mark-v-d/motor_control/software/hal/etherdrive.cpp

#include "rtapi.h"
#ifdef RTAPI
#include "rtapi_app.h"
#endif
#include "hal.h"

static int comp_id;

#ifdef MODULE_INFO
MODULE_INFO(linuxcnc, const_cast<char*>("component:etherdrive:"));
//MODULE_INFO(linuxcnc, const_cast<char*>("pin:out:float:0:out::None:None"));
MODULE_INFO(linuxcnc, const_cast<char*>("param:value:float:0:r::1.0:None"));
MODULE_INFO(linuxcnc, const_cast<char*>("funct:sync:1:"));
MODULE_INFO(linuxcnc, const_cast<char*>("license:GPL"));
MODULE_LICENSE("GPL");
#endif // MODULE_INFO


#include <sys/io.h>

#include "raw_socket.h"
#include "drive_io.h"
#include <vector>

constexpr std::array<uint8_t,6> bcast_mac{255,255,255,255,255,255};
constexpr std::array<uint8_t,4> bcast_ip{255,255,255,255};

std::array<std::array<uint8_t,6>,16> mac;

raw_socket skt;
constexpr uint16_t base=0xec00;

/******************************************************************************/
struct comp_state {
    // input pins
    hal_float_t *Iset[2];
    hal_bit_t *enable;
    hal_bit_t *digout[2];
    hal_u32_t *encoder;
    hal_u32_t *poles;
    hal_float_t *angle_offset;
    hal_float_t *limit[2];
    hal_float_t *P;
    hal_float_t *I;
    hal_float_t *L;
    hal_float_t *overvoltage;
    hal_float_t *overcurrent;

    // output pins
    hal_s32_t *position;
    hal_s32_t *position2;
    hal_s32_t *index;
    hal_s32_t *index2;
    hal_float_t *Irotor[2];
    hal_float_t *Vrotor[2];
    hal_float_t *angle;
    hal_float_t *Vservo;
    hal_u32_t *encoder_invalid;
    hal_u32_t *encoder_missing;
    hal_u32_t *pending;
    hal_u32_t *drive_rx;
    hal_s32_t *timer_delta;
    hal_s32_t *dt;
    hal_bit_t *digin[2];
    hal_u32_t *digin_all;
    hal_bit_t *unconfigured;
    hal_float_t *vthermistor;

    bool valid;
    double thermistor=0;
    static constexpr double thermistor_gain=1e-3;

    void init(int i) {
	std::string prefix="etherdrive."+std::to_string(i)+".";
	auto pin=[&](hal_pin_dir_t dir,std::string name, auto p) {
	    *p=nullptr;
	    using T=decltype(p);
	    if constexpr(std::is_same_v<T,hal_float_t**>)
		return hal_pin_float_new((prefix+name).c_str(),dir,p,comp_id);
	    else if constexpr(std::is_same_v<T,hal_s32_t**>)
		return hal_pin_s32_new((prefix+name).c_str(),dir,p,comp_id);
	    else if constexpr(std::is_same_v<T,hal_u32_t**>)
		return hal_pin_u32_new((prefix+name).c_str(),dir,p,comp_id);
	    else if constexpr(std::is_same_v<T,hal_bit_t**>)
		return hal_pin_bit_new((prefix+name).c_str(),dir,p,comp_id);
	    else
		return 1;
	};
	int ok=
	    !pin(HAL_IN, "Iset-0", &Iset[0]) &&
	    !pin(HAL_IN, "Iset-1", &Iset[1]) &&
	    !pin(HAL_IN, "enable", &enable) &&
	    !pin(HAL_OUT,"position", &position) &&
	    !pin(HAL_OUT,"position2", &position2) &&
	    !pin(HAL_OUT,"index", &index) &&
	    !pin(HAL_OUT,"index2", &index2) &&
	    !pin(HAL_OUT,"Irotor-0", &Irotor[0]) &&
	    !pin(HAL_OUT,"Irotor-1", &Irotor[1]) &&
	    !pin(HAL_OUT,"Vrotor-0", &Vrotor[0]) &&
	    !pin(HAL_OUT,"Vrotor-1", &Vrotor[1]) &&
	    !pin(HAL_OUT,"angle", &angle) &&
	    !pin(HAL_OUT,"Vservo", &Vservo) &&
	    !pin(HAL_OUT,"encoder_invalid", &encoder_invalid) &&
	    !pin(HAL_OUT,"encoder_missing", &encoder_missing) &&
	    !pin(HAL_OUT,"pending", &pending) &&
	    !pin(HAL_OUT,"drive_rx", &drive_rx) &&
	    !pin(HAL_OUT,"timer_delta", &timer_delta) &&
	    !pin(HAL_IN,"digout-0", &digout[0]) &&
	    !pin(HAL_IN,"digout-1", &digout[1]) &&
	    !pin(HAL_OUT,"digin-0", &digin[0]) &&
	    !pin(HAL_OUT,"digin-1", &digin[1]) &&
	    !pin(HAL_OUT,"digin-all", &digin_all) &&
	    !pin(HAL_OUT,"unconfigured", &unconfigured) &&
	    !pin(HAL_OUT,"vthermistor", &vthermistor) &&
	    !pin(HAL_OUT,"timer_error", &dt) &&
	    !pin(HAL_IN,"encoder", &encoder) &&
	    !pin(HAL_IN,"poles", &poles) &&
	    !pin(HAL_IN,"angle_offset", &angle_offset) &&
	    !pin(HAL_IN,"limit-0", &limit[0]) &&
	    !pin(HAL_IN,"limit-1", &limit[1]) &&
	    !pin(HAL_IN,"P", &P) &&
	    !pin(HAL_IN,"I", &I) &&
	    !pin(HAL_IN,"L", &L) &&
	    !pin(HAL_IN,"overvoltage", &overvoltage) &&
	    !pin(HAL_IN,"overcurrent", &overcurrent)
	    ;
	if(ok)
	    *unconfigured=1;
    }

    void update(motion_ns::to_host &buffer){
	*position=buffer.position;
	*index=buffer.index;
	*position2=buffer.position2;
	*index2=buffer.index2;
	*Irotor[0]=buffer.Irotor[0];
	*Irotor[1]=buffer.Irotor[1];
	*Vrotor[0]=buffer.Vrotor[0];
	*Vrotor[1]=buffer.Vrotor[1];
	*angle=buffer.angle;
	*Vservo=buffer.Vservo;
	*encoder_invalid=buffer.encoder_invalid;
	*encoder_missing=buffer.encoder_missing;
	*timer_delta=buffer.timer_delta;
	*digin[0]=!(buffer.digin&1);
	*digin[1]=!((buffer.digin>>1)&1);
	*digin_all=buffer.digin;
	*dt=buffer.timer_error;
	*drive_rx=buffer.counter;
	thermistor+=thermistor_gain*((4095-buffer.tpower)*3.3/4095-thermistor);
	*vthermistor=thermistor;
	(*pending)=0;
    }

    void config_complete() {
	*unconfigured=0;
    }
};

std::vector<comp_state*> state;

static void send(void *p, long period)
{
    for(int i=0; i<state.size(); i++) {
	std::array<uint8_t,4> ip{192,168,0,uint8_t(i+1)};
	auto s=*state[i];
	if((*state[i]->unconfigured)) {
	    config_ns::to_drive d{
		.led=0,
		.encoder=int(*state[i]->encoder),
		.poles=int(*state[i]->poles),
		.angle_offset=float(*state[i]->angle_offset),
		.current_P=float(*state[i]->P),
		.current_I=float(*state[i]->I),
		.current_L=float(*state[i]->L),
		.overvoltage=float(*state[i]->overvoltage),
		.overcurrent=float(*state[i]->overcurrent)
	    };
	    skt.send(config_ns::send_t(skt, mac[i], ip, d));
	    continue;
	}
	std::complex<float> I{
	    float(*state[i]->Iset[0]),
	    float(*state[i]->Iset[1])
	};
	std::complex<float> limit{
	    float(*state[i]->limit[0]),
	    float(*state[i]->limit[1])
	};
	uint32_t dout=*state[i]->digout[0] | (*state[i]->digout[1]<<1);
	if(*state[i]->enable)
	    dout|=motion_ns::to_drive::DRIVE_ENABLE;
	skt.send(motion_ns::send_t(skt, mac[i], ip, I, limit, dout));
	if((*state[i]->pending)>10) {
	    (*state[i]->unconfigured)=1;
	    (*state[i]->pending)=10;
	}
	(*state[i]->pending)++;
    }
}

static void sync(void *p, long period)
{
    static struct timespec timestamp{0,0};
    if(!timestamp.tv_sec) {
	if(clock_gettime(CLOCK_MONOTONIC, &timestamp)) {
	    perror("clock_gettime");
	}
    } else {
	timestamp.tv_nsec+=period;
	while(timestamp.tv_nsec>=1'000'000'000) {
	    timestamp.tv_sec++;
	    timestamp.tv_nsec-=1'000'000'000;
	}
    }

    auto ts=timestamp;
    ts.tv_nsec+=period;
    while(ts.tv_nsec>=1'000'000'000) {
	ts.tv_sec++;
	ts.tv_nsec-=1'000'000'000;
    }

    outb(0,base);
    skt.send(sync_ns::send_t(skt,bcast_mac,bcast_ip,timestamp,ts));
    outb(1,base);

    ssize_t rx_size;
    do {
	union rx_types {
	    udp_t udp;
	    sync_ns::recv_t sync;
	    motion_ns::recv_t motion;
	    char txt[1024];
	} buffer;
	rx_size=recv(skt.socket(), &buffer, sizeof(buffer), MSG_DONTWAIT);
	unsigned index=buffer.udp.src_ip[3]-1;
	if(index>=state.size())
	    continue;
	if(buffer.udp.src_port==htons(motion_ns::port)
	    && rx_size==sizeof(buffer.motion) && index<state.size()
	) {
	    state[index]->update(buffer.motion);
	} else if(buffer.udp.src_port==htons(config_ns::port)) {
	    state[index]->config_complete();
	}
    } while(rx_size>0);
    outb(255,base);
}


////////////////////////////////////////////////////////////////////////////////
static char *names[16] = {0,};
static char const *device="eth1";

RTAPI_MP_STRING(device, "ethernet device");
RTAPI_MP_ARRAY_STRING(names, 16, "mac addresses of etherdrives");

extern "C" int rtapi_app_main(void)
{
    int r = 0;
    int i;
    comp_id = hal_init("etherdrive");
    if(comp_id < 0)
	return comp_id;
    if(ioperm(base, 8, 1)) {
	perror("request_region failed\n");
	return -1;
    }


    for(int i=0; names[i] && i<16; i++) {
	std::array<unsigned,6> d;
	char na[100];
	strcpy(na,names[i]);
	if(sscanf(na,"%x:%x:%x:%x:%x:%x:%x",
	    &d[0],&d[1],&d[2],&d[3],&d[4],&d[5])!=6
	) {
	    rtapi_print_msg(RTAPI_MSG_ERR, "invalid mac address: %s",names[i]);
	    return -EINVAL;
	};
	for(int j=0; j<d.size(); j++) {
	    if(d[j]>255) {
		rtapi_print_msg(RTAPI_MSG_ERR, "invalid mac address: %s",
		    names[i]);
		return -EINVAL;
	    }
	    mac[i][j]=d[j];
	}
        auto p=reinterpret_cast<comp_state*>(hal_malloc(sizeof(comp_state)));
        p->init(i);
	state.push_back(p);
    }

    try {
	skt.init(device);
    } catch (std::string const &s) {
        rtapi_print_msg(RTAPI_MSG_ERR, "Cannot open device");
        return -EINVAL;
    }

    // Export the send-sync function
    if(!r)
	r = hal_export_funct("etherdrive.sync", sync, NULL, 1, 0, comp_id);
    if(!r)
	r = hal_export_funct("etherdrive.send", send, NULL, 1, 0, comp_id);
    if(r) {
        hal_exit(comp_id);
    } else {
        hal_ready(comp_id);
    }
    return r;
}

extern "C" void rtapi_app_exit(void)
{
    hal_exit(comp_id);
}
