mark-v-d/motor_control/software/xmc4400/lathe/lathe_cmds.hal

# Mon Jan 23 14:18:18 CET 2017
#
# This file:    ./lathe_cmds.hal
# Created by:   /usr/src/linuxcnc/lib/hallib/basic_sim.tcl
# With options: 
# From inifile: /home/mark/.emc/lathe.ini
#
# This file contains the hal commands produced by basic_sim.tcl
# (and any hal commands executed prior to its execution).
#
# To use ./lathe_cmds.hal in the original inifile (or a copy of it),
# edit to change:
#     [HAL]
#     HALFILE = LIB:basic_sim.tcl parameters
# to:
#     [HAL]
#     HALFILE = ./lathe_cmds.hal
#
# Note: Inifile Variables substitutions specified in the inifile
#       and interpreted by halcmd are automatically substituted
#       in the created halfile (./lathe_cmds.hal).
#

# user space components
loadusr -W hal_manualtoolchange

# components
loadrt trivkins coordinates=xz 
loadrt motmod base_period_nsec=222222 servo_period_nsec=222222 num_joints=2 
#loadrt __base-thread  (not loaded by loadrt, no args saved)
#loadrt __servo-thread  (not loaded by loadrt, no args saved)
loadrt pid names=J0_pid,J1_pid 
loadrt mux2 names=J0_mux,J1_mux 
loadrt ddt names=J0_vel,J0_accel,J1_vel,J1_accel 
loadrt sim_home_switch names=J0_switch,J1_switch 
loadrt sim_spindle names=sim_spindle 
loadrt limit2 names=limit_speed 
loadrt lowpass names=spindle_mass 
loadrt near names=near_speed 
loadrt etherdrive names=J0_drive,J1_drive ipaddr="192.168.0.5","192.168.0.4"

# pin aliases
# param aliases
# signals
newsig tool:change-loop bit  
# nets
net J0:acc J0_accel.out
net J0:enable joint.0.amp-enable-out => J0_pid.enable
net J0:homesw J0_switch.home-sw => joint.0.home-sw-in
net J0:on-pos J0_pid.output => J0_mux.in1
#net J0:pos-cmd joint.0.motor-pos-cmd => J0_pid.command
net J0:vel J0_vel.out => J0_accel.in

net J1:acc J1_accel.out
net J1:enable joint.1.amp-enable-out => J1_pid.enable
net J1:homesw J1_switch.home-sw => joint.1.home-sw-in
net J1:on-pos J1_pid.output => J1_mux.in1
net J1:pos-cmd joint.1.motor-pos-cmd => J1_pid.command
net J1:pos-fb J1_mux.out => J1_mux.in0 J1_switch.cur-pos J1_vel.in joint.1.motor-pos-fb
net J1:vel J1_vel.out => J1_accel.in

net estop:loop iocontrol.0.user-enable-out => iocontrol.0.emc-enable-in
net sample:enable J0_mux.sel J1_mux.sel motion.motion-enabled
net spindle-at-speed near_speed.out => motion.spindle-at-speed
net spindle-index-enable motion.spindle-index-enable <=> sim_spindle.index-enable
net spindle-pos sim_spindle.position-fb => motion.spindle-revs
net spindle-rpm-filtered spindle_mass.out => motion.spindle-speed-in near_speed.in2
net spindle-speed-cmd motion.spindle-speed-out => limit_speed.in near_speed.in1
net spindle-speed-limited limit_speed.out => sim_spindle.velocity-cmd spindle_mass.in

net tool:change iocontrol.0.tool-change => hal_manualtoolchange.change
net tool:changed hal_manualtoolchange.changed => iocontrol.0.tool-changed
net tool:prep-loop iocontrol.0.tool-prepare => iocontrol.0.tool-prepared
net tool:prep-number iocontrol.0.tool-prep-number => hal_manualtoolchange.number
# parameter values
setp J0_accel.tmax            0
setp J0_mux.tmax            0
setp J0_pid.do-pid-calcs.tmax            0
setp J0_switch.tmax            0
setp J0_vel.tmax            0
setp J1_accel.tmax            0
setp J1_mux.tmax            0
setp J1_pid.do-pid-calcs.tmax            0
setp J1_switch.tmax            0
setp J1_vel.tmax            0
#setp base-thread.tmax            0
setp limit_speed.tmax            0
setp motion-command-handler.tmax            0
setp motion-controller.tmax            0
setp near_speed.difference           10
setp near_speed.scale          1.1
setp near_speed.tmax            0
setp servo-thread.tmax            0
setp sim_spindle.scale   0.01666667
setp sim_spindle.tmax            0
setp spindle_mass.gain         0.07
setp spindle_mass.tmax            0

# realtime thread/function links
addf etherdrive.sync servo-thread
addf motion-command-handler servo-thread
addf motion-controller servo-thread
addf J0_pid.do-pid-calcs servo-thread
addf J1_pid.do-pid-calcs servo-thread
addf J0_mux servo-thread
addf J1_mux servo-thread
addf J0_vel servo-thread
addf J0_accel servo-thread
addf J1_vel servo-thread
addf J1_accel servo-thread
addf J0_switch servo-thread
addf J1_switch servo-thread
addf limit_speed servo-thread
addf spindle_mass servo-thread
addf near_speed servo-thread
addf sim_spindle servo-thread
addf etherdrive.control servo-thread

# setp commands for unconnected input pins
setp J0_pid.FF0 1.0
setp J0_pid.Pgain 0
setp J0_pid.Dgain 0
setp J0_pid.Igain 0
setp J0_pid.FF1 0
setp J0_pid.FF2 0

setp J0_drive.kP-0 0.1
setp J0_drive.kP-1 0.1
setp J0_drive.kI-0 0.1
setp J0_drive.kI-1 0.1

setp J1_pid.FF0 1.0
setp J1_pid.Pgain 0
setp J1_pid.Dgain 0
setp J1_pid.Igain 0
setp J1_pid.FF1 0
setp J1_pid.FF2 0

setp J0_switch.hysteresis 0.05
setp J0_switch.home-pos 0.10
setp J1_switch.hysteresis 0.05
setp J1_switch.home-pos 0.10
setp sim_spindle.scale 0.01666667
setp limit_speed.maxv 5000.0
setp spindle_mass.gain .07
setp near_speed.scale 1.1
setp near_speed.difference 10

setp J1_drive.kP-0 0.1
setp J1_drive.kP-1 0.1
setp J1_drive.kI-0 0.1
setp J1_drive.kI-1 0.1
