mark-v-d/motor_control/software/rt/motion_setpoints.cpp

/*
 *  This program is free software: you can redistribute it and/or modify
 *  it under the terms of the GNU General Public License as published by
 *  the Free Software Foundation, either version 3 of the License, or
 *  (at your option) any later version.
 */

#include <chrono>
#include <complex>
#include <fstream>
#include <iostream>
#include <limits.h>
#include <pthread.h>
#include <sched.h>
#include <sys/io.h>
#include <sys/mman.h>

#include "drive_io.h"
#include "ss.h"

using namespace std::complex_literals;
using namespace std::chrono_literals;

std::array<uint8_t,6> mac{0xc2, 0x00, 0x85, 0x0c, 0x10, 0xc0}; // X
//constexpr std::array<uint8_t,6> mac{0xc2, 0x00, 0x8d, 0x11, 0x11, 0xc0}; // Z
//constexpr std::array<uint8_t,6> mac{0xc2, 0x00, 0x86, 0x05, 0x10, 0xc0}; // T
constexpr std::array<uint8_t,4> ip{192,168,0,6};

constexpr std::complex<float> limit{0.44,0.75};

using timebase_t=std::chrono::duration<int,std::ratio<1,4500>>;

constexpr int order=3;
constexpr int inputs=2;
constexpr int outputs=1;

ss_t<order,inputs,outputs> controller;

std::array<double,2> scale{1,1};

struct sync_I_t:public sync_t {
    std::complex<float> I;
    decltype(controller)::input_t setpoint;
    decltype(controller)::input_t error;
};
std::vector<sync_I_t> table;

std::ostream &operator<<(std::ostream &s, sync_I_t const &d) {
    s	<< sync_t(d)
	<< " " << real(d.I) << " " << imag(d.I)			// 34,35
	<< " " << d.setpoint(0,0) << " " << d.setpoint(1,0)	// 36,37
	<< " " << d.error(0,0) << " " << d.error(1,0)		// 38,39
	<< " " << d.timer_error					// 40
	<< " " << d.counter					// 41
	<< " " << d.timer_delta					// 42
	;
    return s;
}

raw_socket skt("eth1");

void *rt_thread(void *data)
{
    timebase_t time=0s;
    struct timespec ts;
    if(clock_gettime(CLOCK_MONOTONIC, &ts)) {
	perror("clock_gettime");
	return NULL;
    }

    // Use printerport to trigger the scope
    uint16_t base=0xb100;
    if(ioperm(base, 8, 1)) {
	perror("request_region failed\n");
	return NULL;
    }

    int locked=450;

    //decltype(controller)::input_t offset;
    Eigen::Matrix<double,2,1> offset;
    for(size_t i=0; i<table.size(); i++) {
        ////////////////////////////////////////////////////////////////////////
	// timebase and send synchronisation
        ////////////////////////////////////////////////////////////////////////
	time++;
	struct timespec timestamp;
	if(clock_gettime(CLOCK_MONOTONIC, &table[i].timestamp)) {
	    perror("clock_gettime");
	    return NULL;
	}

	ts.tv_nsec+=222222;
	while(ts.tv_nsec>=1'000'000'000) {
	    ts.tv_sec++;
	    ts.tv_nsec-=1'000'000'000;
	}

	skt.send(sync_ns::send_t(skt,mac,ip,table[i].timestamp,ts));

	ssize_t rx_size;
	do{
	    union rx_types {
		udp_t udp;
		sync_ns::recv_t sync;
		motion_ns::recv_t motion;
		char txt[1024];
	    } buffer;
	    rx_size=recv(skt.socket(), &buffer, sizeof(buffer), MSG_DONTWAIT);
	    if(buffer.udp.src_port==htons(sync_ns::port)
		&& rx_size==sizeof(buffer.sync)
	    ) {
		static_cast<sync_ns::to_host&>(table[i])=buffer.sync;
	    } else if(buffer.udp.src_port==htons(motion_ns::port)
		&& rx_size==sizeof(buffer.motion)
	    ) {
		static_cast<motion_ns::to_host&>(table[i])=buffer.motion;
	    }
	} while(rx_size>0);

        ////////////////////////////////////////////////////////////////////////
        // Test specific code
        ////////////////////////////////////////////////////////////////////////
	if(i>0) {
	    decltype(controller)::input_t inputs{
		table[i-1].position/scale[0],
		table[i-1].position2/scale[1]
	    };

	    if(std::abs(table[i].timer_error)>250) {
		i=1;
		locked=450;
	    } else if(locked>0) {
		locked--;
		offset=inputs;
	    } else {
		table[i].error=table[i].setpoint-(inputs-offset);
		auto r=controller.compute(table[i].error);
		table[i].I=1.0if*float(r(0));
	    }
	}
	if(table.size()-i<4500) {
	    table[i].I=0;
	    table[i-1].error=0*offset;
	}
	skt.send(motion_ns::send_t(skt, mac, ip, table[i].I,limit,
	    locked>0? 0:motion_ns::to_drive::DRIVE_ENABLE
	));

        ////////////////////////////////////////////////////////////////////////
        // Wait and receive data
        ////////////////////////////////////////////////////////////////////////
	outb(0,base);
	clock_nanosleep(CLOCK_MONOTONIC, TIMER_ABSTIME, &ts, nullptr);
	outb(0xff,base);

    }
    return NULL;
}

int main(int argc, char *argv[])
{
    if(argc<2)
	return 1;

    {
	std::ifstream settings(argv[1]);
	if(!settings) {
	    perror(argv[1]);
	    return 1;
	}


	std::string s;
	std::getline(settings,s);
	std::array<int,6> m;
	if(sscanf(s.c_str(),"%x:%x:%x:%x:%x:%x",&m[0],&m[1],&m[2],&m[3],&m[4],&m[5])!=6) {
	    std::cout << "Invalid mac address\n";
	    return 1;
	}
	for(int i=0; i<m.size(); i++)
	    mac[i]=m[i];

	controller.read(settings);
	std::vector<double> v;
	while(std::getline(settings,s)) {
	    if(!s.size() || s[0]=='#')
		continue;

	    size_t start=0;
	    while(s.size() && s[0]!='#') {
		try {
		    double d=stod(s,&start);
		    v.push_back(d);
		} catch(std::invalid_argument& ia) {
		    start=s.size();
		}
		s.erase(0,start+1);
	    }
	}
	if(v.size()!=scale.size()) {
	    std::cout << std::format("Scale should have {} values, read {} "
		"values from: {}\n", scale.size(), v.size(), s);
	    return 1;
	}
	for(int i=0;i<scale.size();i++)
	    scale[i]=v[i];
    }

    try {
	std::ifstream setpoints(argv[2]);
	if(!setpoints) {
	    perror(argv[2]);
	    return 1;
	}

	for(int i=0; i<1s/timebase_t(1); i++) // synchronisation for 1s
	    table.emplace_back(sync_I_t{.I=std::complex<float>{0,0}});

	std::string s;
	while(std::getline(setpoints,s)) {
	    if(!s.size() || s[0]=='#')
		continue;
	    decltype(controller)::input_t setpoint;
	    read(setpoint,s);
	    table.emplace_back(sync_I_t{.setpoint=setpoint});
	}

	for(int i=0; i<1s/timebase_t(1); i++) // lead out of 1s
	    table.emplace_back(sync_I_t{.I=std::complex<float>{0,0}});
    } catch(std::string err) {
	std::cout << err;
	return 1;
    }


    /* Lock memory */
    if(mlockall(MCL_CURRENT|MCL_FUTURE) == -1) {
	    printf("mlockall failed: %m\n");
	    exit(-2);
    }

    /* Initialize pthread attributes (default values) */
    pthread_attr_t attr;
    int ret=pthread_attr_init(&attr);
    if(ret) {
	    printf("init pthread attributes failed\n");
	    goto out;
    }
    /* Set a specific stack size  */
    ret=pthread_attr_setstacksize(&attr, PTHREAD_STACK_MIN);
    if(ret) {
	printf("pthread setstacksize failed\n");
	goto out;
    }
    /* Set scheduler policy and priority of pthread */
    ret=pthread_attr_setschedpolicy(&attr, SCHED_FIFO);
    if(ret) {
	    printf("pthread setschedpolicy failed\n");
	    goto out;
    }
    struct sched_param param;
    param.sched_priority=80;
    ret = pthread_attr_setschedparam(&attr, &param);
    if (ret) {
	    printf("pthread setschedparam failed\n");
	    goto out;
    }
    /* Use scheduling parameters of attr */
    ret = pthread_attr_setinheritsched(&attr, PTHREAD_EXPLICIT_SCHED);
    if (ret) {
	    printf("pthread setinheritsched failed\n");
	    goto out;
    }
    /* Create a pthread with specified attributes */
    pthread_t thread;
    ret = pthread_create(&thread, &attr, rt_thread, NULL);
    if (ret) {
	    printf("create pthread failed\n");
	    goto out;
    }
    /* Join the thread and wait until it is done */
    ret = pthread_join(thread, NULL);
    if (ret)
	    printf("join pthread failed: %m\n");
    for(auto &x: table)
	std::cout << x << std::endl;
out:
    return ret;
}
