mark-v-d/motor_control/software/alpha/gmoccapy_postgui.hal

###################################################################
#        moccapy_postgui.hal file from Norbert Schechner          #
###################################################################
# 
# net S0:at_speed gmoccapy.spindle_at_speed_led
# net S0:speed_rpm speed_controller.0.speed_rpm => gmoccapy.spindle_feedback_bar
# 
# # the unlink pin commands are only used, because they are connected
# # in core_sim.hal and we use this file to simulate
# unlinkp iocontrol.0.tool-change
# unlinkp iocontrol.0.tool-changed
# unlinkp iocontrol.0.tool-prep-number
# 
# net tool-change      gmoccapy.toolchange-change   <=  iocontrol.0.tool-change
# net tool-changed     gmoccapy.toolchange-changed  <=  iocontrol.0.tool-changed
# net tool-prep-number gmoccapy.toolchange-number   <=  iocontrol.0.tool-prep-number
# 
# net tooloffset-x  gmoccapy.tooloffset-x  <=  motion.tooloffset.x
# net tooloffset-z  gmoccapy.tooloffset-z  <=  motion.tooloffset.z
# 
# ################################################################################
setp thermistor.0.t0-c 25
setp thermistor.1.t0-c 25
setp thermistor.0.r0 47000
setp thermistor.1.r0 47000
setp thermistor.0.beta 3952
setp thermistor.1.beta 3952
setp thermistor.0.r-other 2000
setp thermistor.1.r-other 2000
setp thermistor.0.v-total 3.3
setp thermistor.1.v-total 3.3
net Vtherm-0 etherdrive.0.vthermistor => thermistor.0.v-thermistor
net Vtherm-1 etherdrive.1.vthermistor => thermistor.1.v-thermistor

# # 
# #  15 top keys
# # 
# net v2 input.0.btn-task => gmoccapy.v-button.button-2
# net v3 input.0.btn-back => gmoccapy.v-button.button-3
# net v4 input.0.btn-forward => gmoccapy.v-button.button-4
# net v5 input.0.btn-extra => gmoccapy.v-button.button-5
# net v6 input.0.btn-side => gmoccapy.v-button.button-6
# net h0 input.0.key-287 => gmoccapy.h-button.button-0
# net h1 input.0.key-286 => gmoccapy.h-button.button-1
# net h2 input.0.key-285 => gmoccapy.h-button.button-2
# net h3 input.0.key-284 => gmoccapy.h-button.button-3
# net h4 input.0.key-283 => gmoccapy.h-button.button-4
# net h5 input.0.btn-base2 => gmoccapy.h-button.button-5
# net h6 input.0.btn-base => gmoccapy.h-button.button-6
# net h7 input.0.btn-pinkie => gmoccapy.h-button.button-7
# net h8 input.0.btn-top2 => gmoccapy.h-button.button-8
# net h9 input.0.btn-top => gmoccapy.h-button.button-9
# 
# 
# #####################################
# # Potmeters/diy buttons
# #####################################
# net spindle_override input.0.abs-ry-position => gmoccapy.spindle.spindle-override.direct-value
# setp gmoccapy.spindle.spindle-override.analog-enable 1
# 
# net feed_override input.0.abs-rz-position => gmoccapy.feed.feed-override.direct-value
# setp gmoccapy.feed.feed-override.analog-enable 1
# 
# net rapid_override input.0.abs-rx-position => gmoccapy.rapid.rapid-override.direct-value
# setp gmoccapy.rapid.rapid-override.analog-enable 1
# 
# net jog_override input.0.abs-z-position => gmoccapy.jog.jog-velocity.direct-value
# setp gmoccapy.jog.jog-velocity.analog-enable 1
# 
# setp input.0.abs-rx-offset 0 
# setp input.0.abs-rx-scale 4000 
# setp input.0.abs-rx-fuzz 8
# setp input.0.abs-ry-offset 0 
# setp input.0.abs-ry-scale 4000 
# setp input.0.abs-ry-fuzz 8
# setp input.0.abs-rz-offset 0 
# setp input.0.abs-rz-scale 4000 
# setp input.0.abs-rz-fuzz 8
# setp input.0.abs-z-offset 0 
# setp input.0.abs-z-scale 4000 
# setp input.0.abs-z-fuzz 8
# 
# net spindle_forward  input.0.btn-thumb2 => halui.spindle.0.forward
# net spindle_stop  input.0.btn-thumb => halui.program.stop
# net spindle_reverse  input.0.btn-trigger => halui.spindle.0.reverse
# 
# net v1 input.0.btn-left => gmoccapy.v-button.button-1
# net mist-on-off input.0.btn-middle 
# net macro1 input.0.key-280 => halui.mdi-command-01
# net button-start-pause input.0.key-281
# net z_0 input.0.key-282 => halui.mdi-command-14
# 
# #### State for coolant
# loadrt multiswitch cfg=2
# loadrt and2 count=1
# net mist-on-off => multiswitch.0.up
# net mist-off multiswitch.0.bit-00 => and2.0.in0
# net mist-on multiswitch.0.bit-01 => halui.mist.on
# net machine-is-on halui.machine.is-on => and2.0.in1
# net mist-off2 and2.0.out => halui.mist.off
# 
# addf multiswitch.0 servo-thread
# addf and2.0 servo-thread
# 
# loadrt flipflop names=flipflop_resume,flipflop_pause,flipflop_run
# addf flipflop_resume servo-thread
# addf flipflop_pause servo-thread
# addf flipflop_run servo-thread
# 
# net button-start-pause  => flipflop_pause.clk flipflop_resume.clk flipflop_run.clk
# net is-paused halui.program.is-paused => flipflop_resume.data flipflop_pause.reset
# net is-running halui.program.is-running => flipflop_pause.data flipflop_run.reset flipflop_resume.reset
# net is-idle halui.program.is-idle => flipflop_run.data
# net resume flipflop_resume.out => halui.program.resume
# net pause flipflop_pause.out => halui.program.pause
# net run flipflop_run.out => halui.mode.auto halui.program.run 
# 
# #net machine-is-on => input.0.led-scrolll
# net spindle-fw halui.spindle.0.runs-forward => input.0.led-charging
# net spindle-bw halui.spindle.0.runs-backward =>  input.0.led-misc
# 
# loadrt pwmgen output_type=0
# addf pwmgen.update servo-thread
# addf pwmgen.make-pulses servo-thread
# setp pwmgen.0.pwm-freq 1
# setp pwmgen.0.value 0.5
# net is-paused => pwmgen.0.enable 
# loadrt or2 count=1
# addf or2.0 servo-thread
# net pause-pulse pwmgen.0.pwm => or2.0.in0
# net is-running => or2.0.in1
# net green-led or2.0.out => input.0.led-suspend
# 
# net led-manual halui.mode.is-manual => input.0.led-kana
# net led-mdi halui.mode.is-mdi => input.0.led-compose
# net led-auto halui.mode.is-auto => input.0.led-scrolll
# net led-setup gmoccapy.mode_setup => input.0.led-numl
