mark-v-d/motor_control/software/lathe_config/spindle_load.hal

net S0:current-display speed_controller.0.I_fb => spindle_load.spindle_current
net S0:temperature-display thermistor.2.temperature-c => spindle_load.drive_temperature
