mark-v-d/motor_control/software/xmc4400/src/xmc_eth_phy_ksz8031rnl.c

/**
 * @file xmc_eth_phy_ksz8031ml.c
 * @date 2015-12-15 
 *
 * @cond
 *********************************************************************************************************************
 * XMClib v2.1.6 - XMC Peripheral Driver Library
 *
 * Copyright (c) 2015-2016, Infineon Technologies AG
 * All rights reserved.                        
 *                                             
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
 * Neither the name of the copyright holders nor the names of its contributors may be used to endorse or promote 
 * products derived from this software without specific prior written permission.                                           
 *                                                                              
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
 * To improve the quality of the software, users are encouraged to share modifications, enhancements or bug fixes with 
 * Infineon Technologies AG dave@infineon.com).                                                          
 *********************************************************************************************************************
 *
 * Change History
 * --------------
 *
 * 2015-06-20:
 *     - Initial
 *
 * 2015-12-15:
 *     - Added Reset and exit power down
 *     - Reset function called in Init function
 *
 * @endcond
 */

/*******************************************************************************
 * HEADER FILES
 *******************************************************************************/

#include <xmc_eth_phy.h>

/*******************************************************************************
 * MACROS
 *******************************************************************************/

/* Basic Registers */
#define REG_BMCR                (0x00U)        /* Basic Mode Control Register       */
#define REG_BMSR                (0x01U)        /* Basic Mode Status Register        */
#define REG_PHYIDR1             (0x02U)        /* PHY Identifier 1                  */
#define REG_PHYIDR2             (0x03U)        /* PHY Identifier 2                  */
#define REG_ANAR                (0x04U)        /* Auto-Negotiation Advertisement    */
#define REG_ANLPAR              (0x05U)        /* Auto-Neg. Link Partner Abitily    */
#define REG_ANER                (0x06U)        /* Auto-Neg. Expansion Register      */
#define REG_ANNPTR              (0x07U)        /* Auto-Neg. Next Page TX            */

/* Extended Registers */
#define REG_PHYCTRL1            (0x1eU)        /* PHY control 1 Register            */

/* Basic Mode Control Register */
#define BMCR_RESET              (0x8000U)      /* Software Reset                    */
#define BMCR_LOOPBACK           (0x4000U)      /* Loopback mode                     */
#define BMCR_SPEED_SEL          (0x2000U)      /* Speed Select (1=100Mb/s)          */
#define BMCR_ANEG_EN            (0x1000U)      /* Auto Negotiation Enable           */
#define BMCR_POWER_DOWN         (0x0800U)      /* Power Down                        */
#define BMCR_ISOLATE            (0x0400U)      /* Isolate Media interface           */
#define BMCR_REST_ANEG          (0x0200U)      /* Restart Auto Negotiation          */
#define BMCR_DUPLEX             (0x0100U)      /* Duplex Mode (1=Full duplex)       */
#define BMCR_COL_TEST           (0x0080U)      /* Collision Test                    */

/* Basic Mode Status Register */
#define BMSR_100B_T4            (0x8000U)      /* 100BASE-T4 Capable                */
#define BMSR_100B_TX_FD         (0x4000U)      /* 100BASE-TX Full Duplex Capable    */
#define BMSR_100B_TX_HD         (0x2000U)      /* 100BASE-TX Half Duplex Capable    */
#define BMSR_10B_T_FD           (0x1000U)      /* 10BASE-T Full Duplex Capable      */
#define BMSR_10B_T_HD           (0x0800U)      /* 10BASE-T Half Duplex Capable      */
#define BMSR_MF_PRE_SUP         (0x0040U)      /* Preamble suppression Capable      */
#define BMSR_ANEG_COMPL         (0x0020U)      /* Auto Negotiation Complete         */
#define BMSR_REM_FAULT          (0x0010U)      /* Remote Fault                      */
#define BMSR_ANEG_ABIL          (0x0008U)      /* Auto Negotiation Ability          */
#define BMSR_LINK_STAT          (0x0004U)      /* Link Status (1=established)       */
#define BMSR_JABBER_DET         (0x0002U)      /* Jaber Detect                      */
#define BMSR_EXT_CAPAB          (0x0001U)      /* Extended Capability               */

/* PHY control 1 Register */
#define PHYCTRL1_OPMODE_SPEED   (0x0003U)
#define PHYCTRL1_OPMODE_DUPLEX  (0x0004U)

/* PHY Identifier Registers */
#define PHY_ID1                 (0x0022U)      /* KSZ8031 Device Identifier MSB */
#define PHY_ID2                 (0x1550U)      /* KSZ8031 Device Identifier LSB */

/*******************************************************************************
 * API IMPLEMENTATION
 *******************************************************************************/

 /* Check if the device identifier is valid */
static int32_t XMC_ETH_PHY_IsDeviceIdValid(XMC_ETH_MAC_t *const eth_mac, uint8_t phy_addr)
{
  uint16_t phy_id1;
  uint16_t phy_id2;
  XMC_ETH_PHY_STATUS_t status;

  /* Check Device Identification. */
  if ((XMC_ETH_MAC_ReadPhy(eth_mac, phy_addr, REG_PHYIDR1, &phy_id1) == XMC_ETH_MAC_STATUS_OK) &&
      (XMC_ETH_MAC_ReadPhy(eth_mac, phy_addr, REG_PHYIDR2, &phy_id2) == XMC_ETH_MAC_STATUS_OK))
  {
    if ((phy_id1 == PHY_ID1) && ((phy_id2 & (uint16_t)0xfff0) == PHY_ID2))
    {
      status = XMC_ETH_PHY_STATUS_OK;
    }
    else
    {
      status = XMC_ETH_PHY_STATUS_ERROR_DEVICE_ID;
    }
  }
  else
  {
    status = XMC_ETH_PHY_STATUS_ERROR_TIMEOUT;
  }

  return (int32_t)status;
}

/* PHY initialize */
int32_t XMC_ETH_PHY_Init(XMC_ETH_MAC_t *const eth_mac, uint8_t phy_addr, const XMC_ETH_PHY_CONFIG_t *const config)
{
  int32_t status;
  uint16_t reg_bmcr;

  status = XMC_ETH_PHY_IsDeviceIdValid(eth_mac, phy_addr);
  
  if (status == (int32_t)XMC_ETH_PHY_STATUS_OK)
  {
    status = XMC_ETH_PHY_Reset(eth_mac, phy_addr);
    
    if (status == (int32_t)XMC_ETH_PHY_STATUS_OK)
    {
      reg_bmcr = 0U;
      if (config->speed == XMC_ETH_LINK_SPEED_100M)
      {
        reg_bmcr |= BMCR_SPEED_SEL;
      }

      if (config->duplex == XMC_ETH_LINK_DUPLEX_FULL)
      {
        reg_bmcr |= BMCR_DUPLEX;
      }

      if (config->enable_auto_negotiate == true)
      {
        reg_bmcr |= BMCR_ANEG_EN;
      }

      if (config->enable_loop_back == true)
      {
        reg_bmcr |= BMCR_LOOPBACK;
      }

      status = (int32_t)XMC_ETH_MAC_WritePhy(eth_mac, phy_addr, REG_BMCR, reg_bmcr);
    }
  }

  return status;
}

/* Reset */
int32_t XMC_ETH_PHY_Reset(XMC_ETH_MAC_t *const eth_mac, uint8_t phy_addr)
{
  int32_t status;
  uint16_t reg_bmcr;

  /* Reset PHY*/
  status = (int32_t)XMC_ETH_MAC_WritePhy(eth_mac, phy_addr, REG_BMCR, BMCR_RESET);
  if (status == (int32_t)XMC_ETH_PHY_STATUS_OK)
  {      
    /* Wait for the reset to complete */
    do 
    {
      status = XMC_ETH_MAC_ReadPhy(eth_mac, phy_addr, REG_BMCR, &reg_bmcr);
    } while ((reg_bmcr & BMCR_RESET) != 0);
  }
    
  return status;
}

/* Initiate power down */
int32_t XMC_ETH_PHY_PowerDown(XMC_ETH_MAC_t *const eth_mac, uint8_t phy_addr)
{
  int32_t status;
  uint16_t reg_bmcr;

  status = XMC_ETH_MAC_ReadPhy(eth_mac, phy_addr, REG_BMCR, &reg_bmcr);
  if (status == (int32_t)XMC_ETH_PHY_STATUS_OK)
  {      
    reg_bmcr |= BMCR_POWER_DOWN;
    status = (int32_t)XMC_ETH_MAC_WritePhy(eth_mac, phy_addr, REG_BMCR, reg_bmcr);
  }
  return status;
}

/* Exit power down */
int32_t XMC_ETH_PHY_ExitPowerDown(XMC_ETH_MAC_t *const eth_mac, uint8_t phy_addr)
{
  int32_t status;
  uint16_t reg_bmcr;

  status = XMC_ETH_MAC_ReadPhy(eth_mac, phy_addr, REG_BMCR, &reg_bmcr);  
  if (status == (int32_t)XMC_ETH_PHY_STATUS_OK)
  {      
    reg_bmcr &= ~BMCR_POWER_DOWN;
    status = (int32_t)XMC_ETH_MAC_WritePhy(eth_mac, phy_addr, REG_BMCR, reg_bmcr);
  }
  return status;
}

/* Get link status */
XMC_ETH_LINK_STATUS_t XMC_ETH_PHY_GetLinkStatus(XMC_ETH_MAC_t *const eth_mac, uint8_t phy_addr)
{
  uint16_t val;

  XMC_ETH_MAC_ReadPhy(eth_mac, phy_addr, REG_BMSR, &val);

  return (XMC_ETH_LINK_STATUS_t)((val & BMSR_LINK_STAT) ? XMC_ETH_LINK_STATUS_UP : XMC_ETH_LINK_STATUS_DOWN);
}

/* Get link speed */
XMC_ETH_LINK_SPEED_t XMC_ETH_PHY_GetLinkSpeed(XMC_ETH_MAC_t *const eth_mac, uint8_t phy_addr)
{
  uint16_t val;

  XMC_ETH_MAC_ReadPhy(eth_mac, phy_addr, REG_PHYCTRL1, &val);

  return (XMC_ETH_LINK_SPEED_t)(((val & PHYCTRL1_OPMODE_SPEED) - 1U) ? XMC_ETH_LINK_SPEED_100M : XMC_ETH_LINK_SPEED_10M);
}

/* Get link duplex settings */
XMC_ETH_LINK_DUPLEX_t XMC_ETH_PHY_GetLinkDuplex(XMC_ETH_MAC_t *const eth_mac, uint8_t phy_addr)
{
  uint16_t val;

  XMC_ETH_MAC_ReadPhy(eth_mac, phy_addr, REG_PHYCTRL1, &val);

  return (XMC_ETH_LINK_DUPLEX_t)((val & PHYCTRL1_OPMODE_DUPLEX) ? XMC_ETH_LINK_DUPLEX_FULL : XMC_ETH_LINK_DUPLEX_HALF);
}
