mark-v-d/motor_control/software/rt/raw_socket.h

#ifndef RAW_SOCKET_H
#define RAW_SOCKET_H

#include <stdio.h>
#include <string.h>
#include <stdlib.h>
#include <sys/ioctl.h>
#include <sys/socket.h>
#include <arpa/inet.h>
#include <linux/if_packet.h>
#include <net/if.h>
#include <netinet/ether.h>

#include <string>
#include <array>
using namespace std::string_literals;

class raw_socket {
    static constexpr uint16_t ETHER_TYPE=0x0800;
    int rxs;
public:
    struct sockaddr_ll socket_address;
    std::array<uint8_t,6> src_mac;
    std::array<uint8_t,4> src_ip{192,168,0,253};

public:
    raw_socket() { rxs=-1; }

    raw_socket(char const *name) { init(name); }

    void init(char const *name) {
	rxs = ::socket(AF_PACKET, SOCK_RAW, htons(ETHER_TYPE));
	if(rxs==-1) {
	    perror("receive socket");
	    exit(1);
	}

	/* Get the index of the interface to send on */
	char ifName[IFNAMSIZ];
	memset(ifName,0,sizeof(ifName));
	strncpy(ifName,name,sizeof(ifName));

	int sockopt;
	if(setsockopt(rxs, SOL_SOCKET, SO_REUSEADDR,&sockopt,sizeof sockopt)<0)
	    throw("setsockopt"s);
	/* Bind to device */
	if(setsockopt(rxs, SOL_SOCKET, SO_BINDTODEVICE, ifName, IFNAMSIZ-1)<0)
	    throw("SO_BINDTODEVICE"s);

	struct ifreq if_idx;
	memset(if_idx.ifr_name,0,sizeof(if_idx.ifr_name));
	strncpy(if_idx.ifr_name, name, sizeof(if_idx.ifr_name));
	if(ioctl(rxs, SIOCGIFINDEX, &if_idx) < 0)
	    throw("SIOCGIFINDEX"s);
	socket_address.sll_ifindex = if_idx.ifr_ifindex;
	socket_address.sll_halen = ETH_ALEN;

	/* Get the MAC address of the interface to send on */
	if (ioctl(rxs, SIOCGIFHWADDR, &if_idx) < 0)
	    throw("SIOCGIFHWADDR"s);
	src_mac={
	    ((uint8_t *)&if_idx.ifr_hwaddr.sa_data)[0],
	    ((uint8_t *)&if_idx.ifr_hwaddr.sa_data)[1],
	    ((uint8_t *)&if_idx.ifr_hwaddr.sa_data)[2],
	    ((uint8_t *)&if_idx.ifr_hwaddr.sa_data)[3],
	    ((uint8_t *)&if_idx.ifr_hwaddr.sa_data)[4],
	    ((uint8_t *)&if_idx.ifr_hwaddr.sa_data)[5]
	};
    }

    template <class T>
    int send(T const &pkt) {
	if(rxs<0)
	    return -1;
	return sendto(rxs, &pkt, sizeof(pkt), MSG_DONTWAIT,
	    (struct sockaddr*)&socket_address, sizeof(socket_address) );
    }

    int socket() { return rxs; }
};

#endif
