mark-v-d/motor_control/software/xmc4400/src/icmp.cpp

#include "icmp.h"
#include <algorithm>

using namespace std;
icmp_echo_t icmpProcessing::pkt __attribute__((section ("ETH_RAM")));

void icmpProcessing::Received(
    Ethernet *eth,
    Ethernet::descriptor const &desc
) {
    pkt=desc.buffer->icmp_echo;
    itm.PORT[3].u32=pkt.type;
    switch(pkt.type) {
    case icmp_t::ECHO:
	itm.PORT[4].u32=__LINE__;
	eth->set_ipv4_address(pkt.dst_ip);
	pkt.dst_mac=pkt.src_mac;
	pkt.dst_ip=pkt.src_ip;
	eth->set_saddr(&pkt);

	pkt.type=0; // ICMP_ECHO_REPLY;
	pkt.ipv4_checksum=0;
	pkt.icmp_checksum=0;
	itm.PORT[4].u32=__LINE__;
	eth->transmit(this,&pkt,(0x3fff&(desc.status>>16))-4);
	itm.PORT[4].u32=__LINE__;
	break;
    case icmp_t::UNREACHABLE: {
	auto pkt=desc.buffer->icmp_unreachable_udp;
	if(pkt.ipv4.protocol==ipv4_t::UDP)
	    eth->Unreachable_udp(pkt.udp.dst_port);
	} break;
    }
}

void icmpProcessing::Transmitted(
    Ethernet *eth,
    Ethernet::descriptor const &desc
) {
}
